markus-marandi/DCSupplyHub/electronics/simulations/Part 1 Circuit.asc

C1: cap; 0.1µ
C2: cap; 0.1µ
C3: cap; 100n
C4: cap; 0.1µ
Q1: npn; 2N3904
Q2: npn; 2N3904
R1: res; 1k
R2: res; 1k
R3: res; 1k
R4: res; 1k
R5: res; 1k
R6: res; 1k
R7: res; 100
R8: res; 1k
R9: res; 18k
R10: res; 18k
R11: res; 1k
U1: opamp2; LM358
U2: opamp2; LM358
V1: voltage; 30
Named nets: 0, V++, VSET, ISET, CL_CP, CLIM
.inc LM358.txt
.tran .1
